Ehryk/NameShield/Documentation/Pictures/1 - Fritzing PCBs.jpg

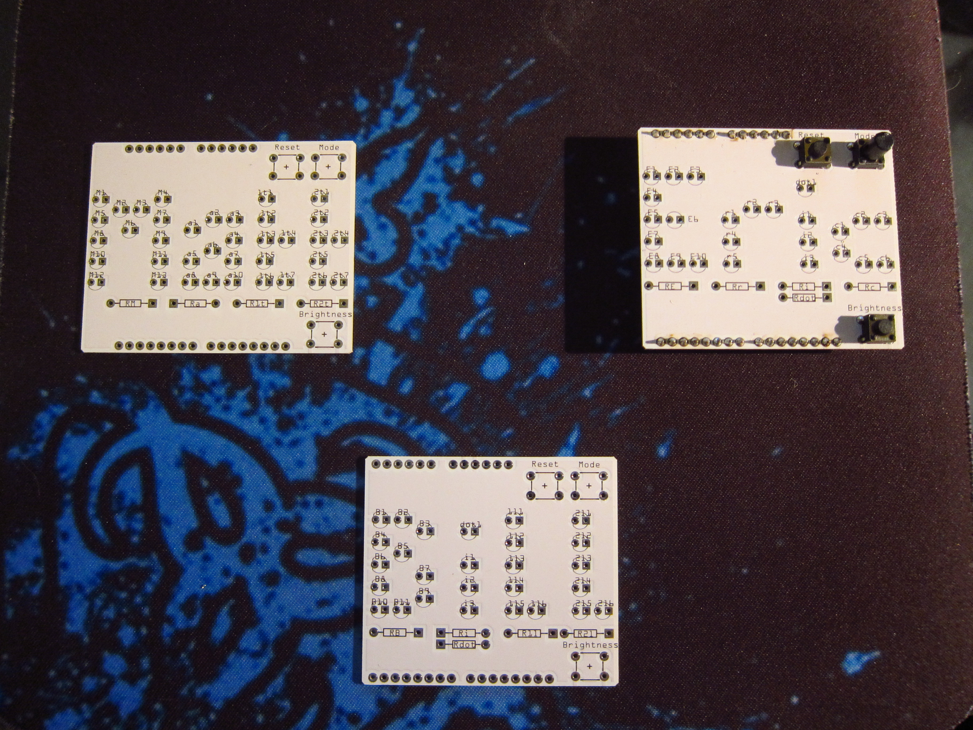
Documentation/Pictures/1 - Fritzing PCBs.jpg
