Ehryk/NameShield/Documentation/Pictures/3 - Finished Eric.jpg

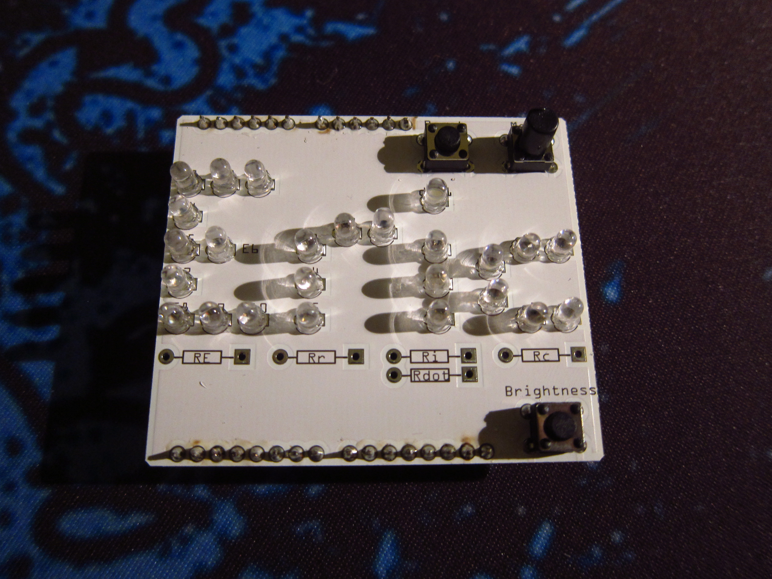
Documentation/Pictures/3 - Finished Eric.jpg
