Ehryk/NameShield/Documentation/Pictures/5 - Finished Eric, Matt, Bill.jpg

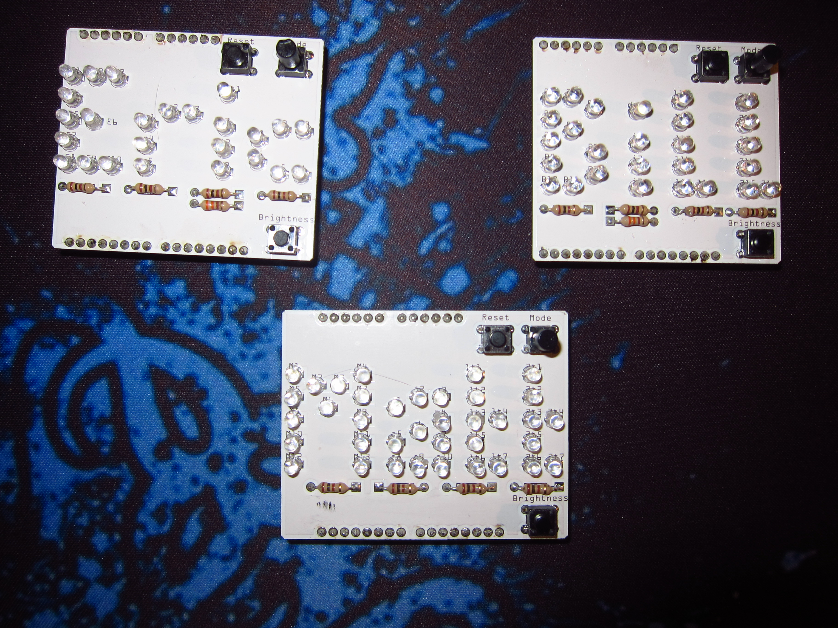
Documentation/Pictures/5 - Finished Eric, Matt, Bill.jpg
