Ehryk/NameShield/Documentation/Pictures/6 - Eric LEDs On.jpg

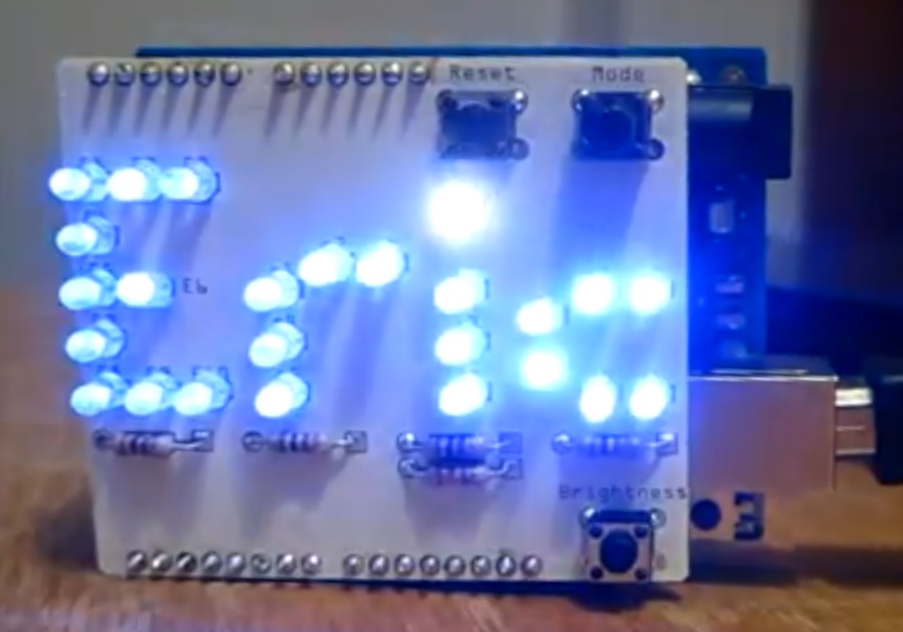
Documentation/Pictures/6 - Eric LEDs On.jpg
