Ehryk/NameShield/Documentation/Pictures/7 - Bill LEDs On.jpg

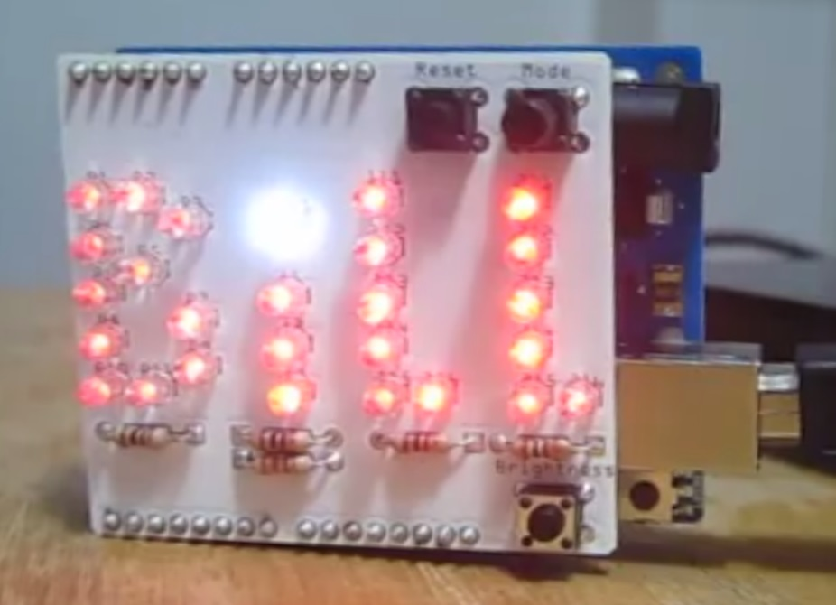
Documentation/Pictures/7 - Bill LEDs On.jpg
