Ehryk/NameShield/Documentation/Pictures/9 - Eric on Diavolino.jpg

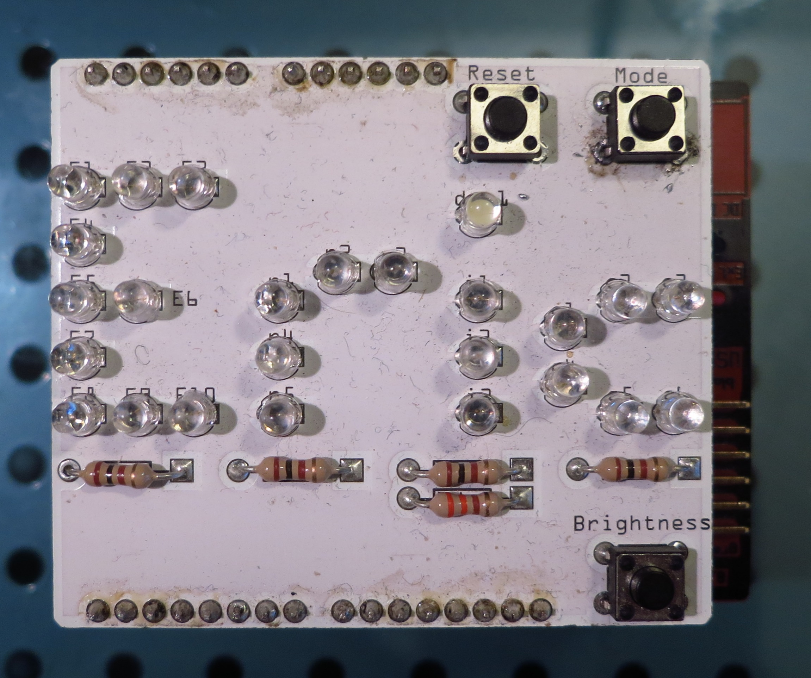
Documentation/Pictures/9 - Eric on Diavolino.jpg
