Ehryk/NameShield/Documentation/Pictures/Circuit/Electret Microphone - Simple.png

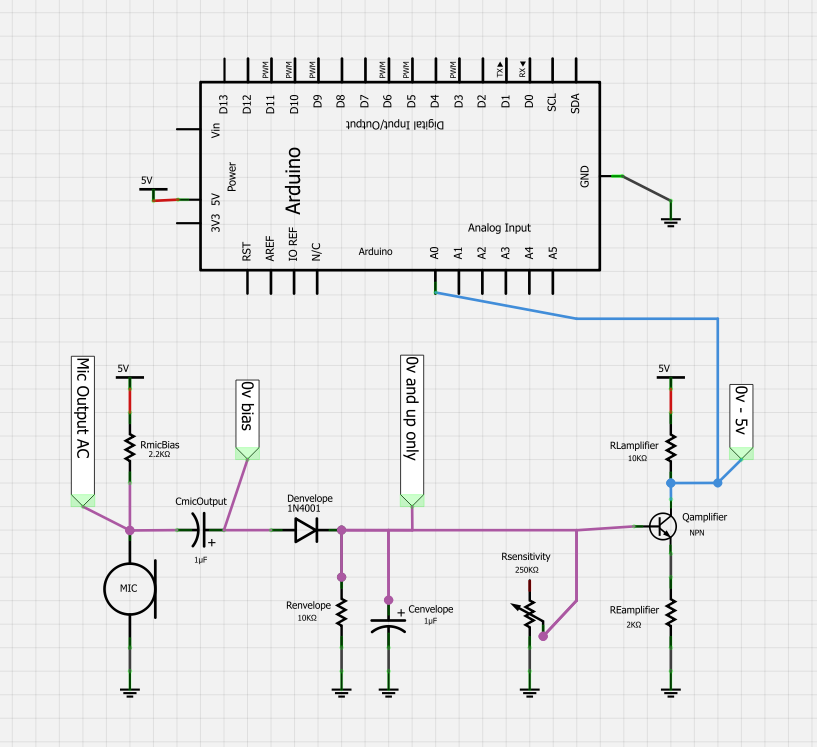
Documentation/Pictures/Circuit/Electret Microphone - Simple.png
