Ehryk/NameShield/Documentation/Pictures/RDI 1 - Empty Front.jpg

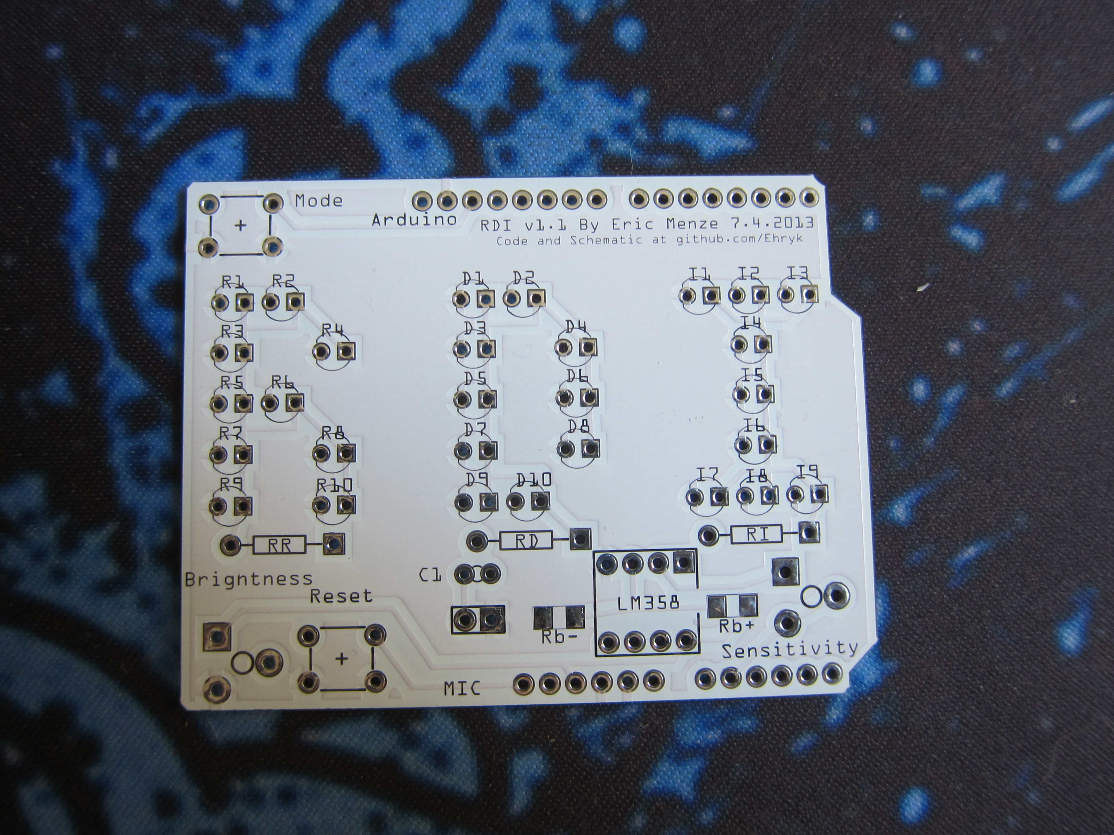
Documentation/Pictures/RDI 1 - Empty Front.jpg
