Ehryk/NameShield/Documentation/Pictures/RDI 2 - Empty Back.jpg

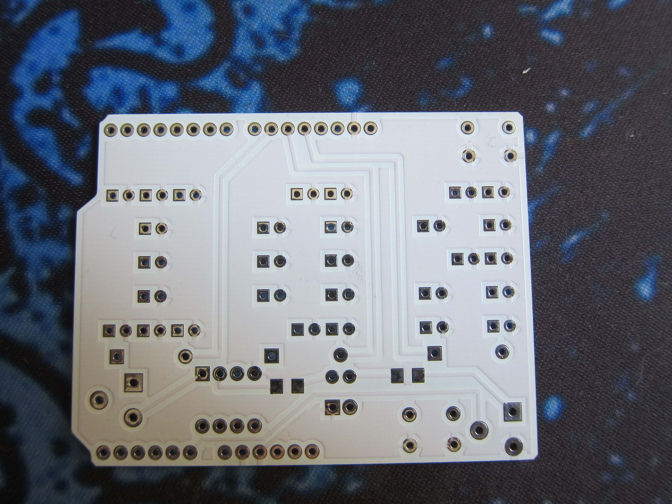
Documentation/Pictures/RDI 2 - Empty Back.jpg
