Ehryk/NameShield/Documentation/Pictures/RDI 4 - Populated Back.jpg

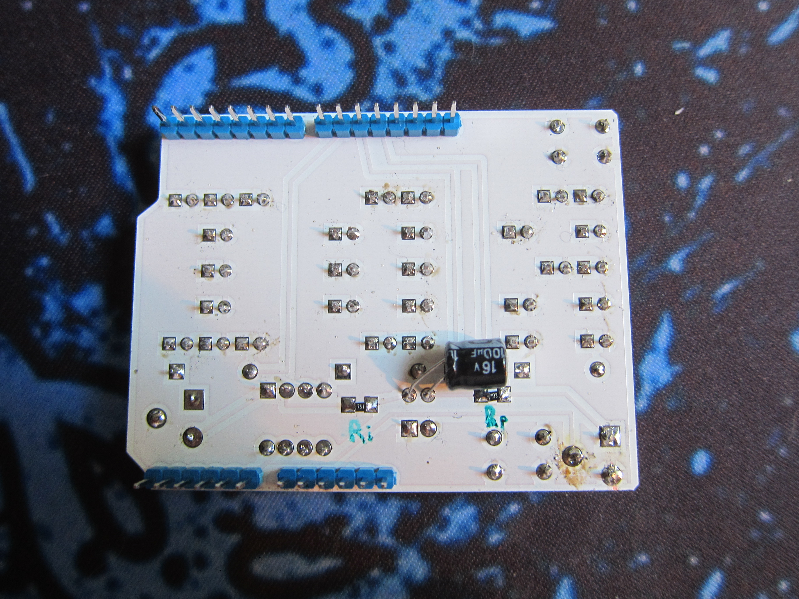
Documentation/Pictures/RDI 4 - Populated Back.jpg
