Ehryk/NameShield/Documentation/Pictures/RDI 5 - LEDs On.jpg

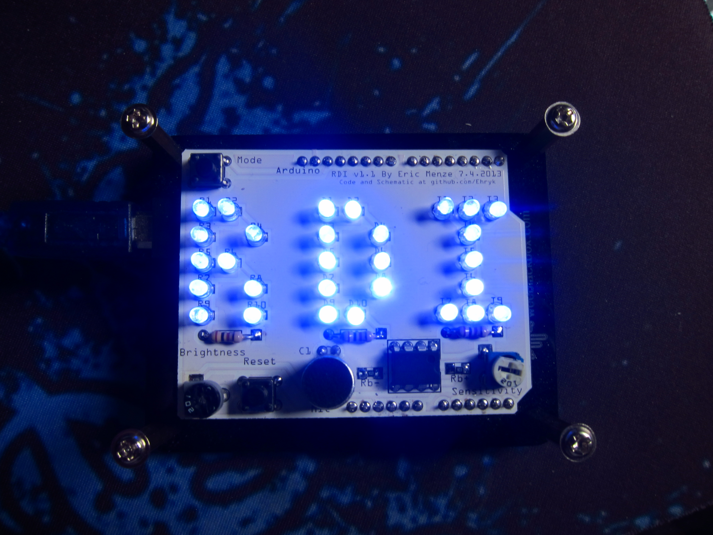
Documentation/Pictures/RDI 5 - LEDs On.jpg
